gabipintea/picomotion/3D/PicoMotion-2021-01 (1).png

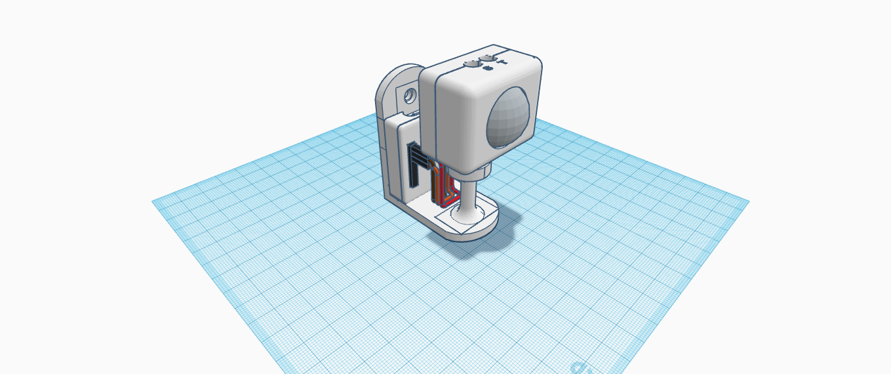
3D/PicoMotion-2021-01 (1).png
