gabipintea/picomotion/3D/PicoMotion-2021-01 (2).png

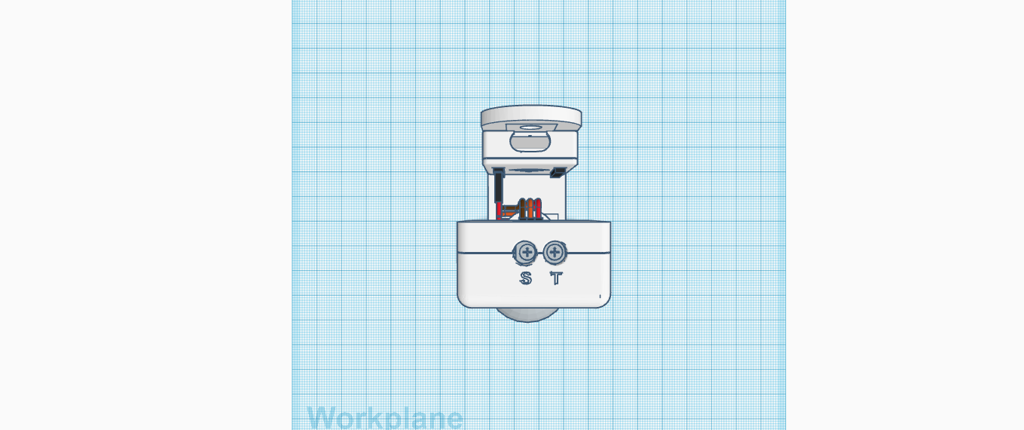
3D/PicoMotion-2021-01 (2).png
