gabipintea/picomotion/3D/PicoMotion-2021-01 (6).png

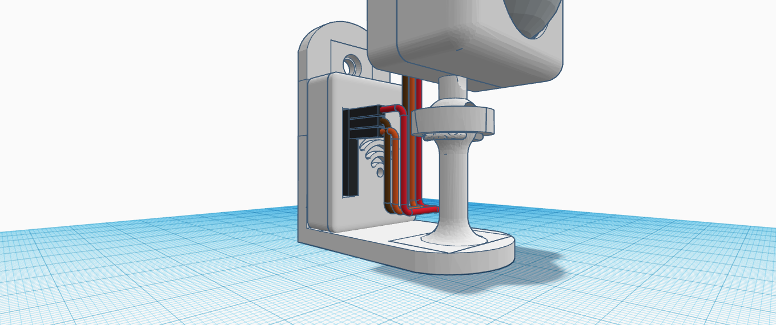
3D/PicoMotion-2021-01 (6).png
