gabipintea/picomotion/3D/PicoMotion-2021-01 (8).png

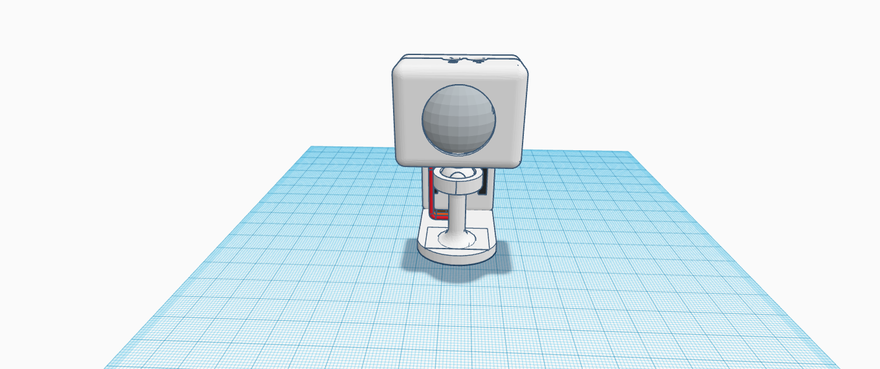
3D/PicoMotion-2021-01 (8).png
