gabipintea/picomotion/3D/PicoMotion-2021-01 (10).png

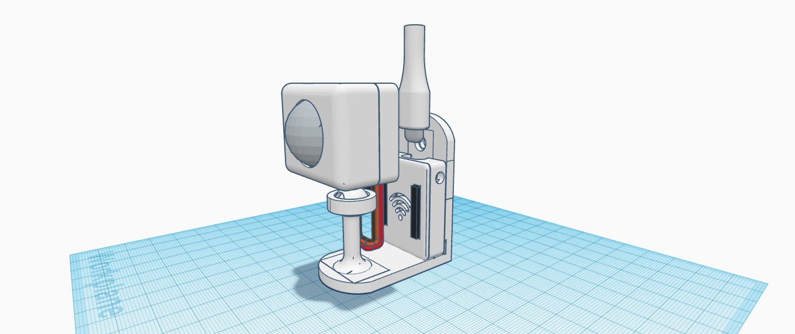
3D/PicoMotion-2021-01 (10).png
